BasementBuilds/RobotHandV2/Github STLs/wideWinchThumb (1).stl

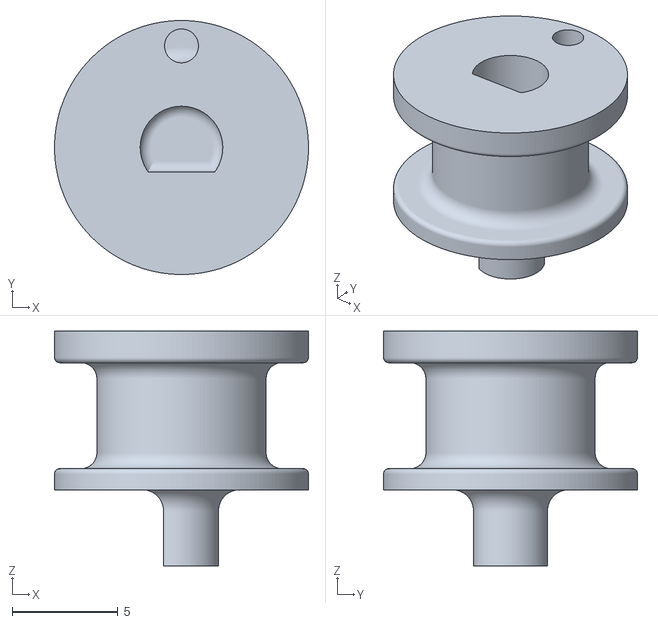
[picture p31: CAD file, 2025-12-30]
Github STLs/wideWinchThumb (1).stl
12.0 x 12.0 x 11.1
