BasementBuilds/RobotHandV2/Github STLs/tpuDigits.stl

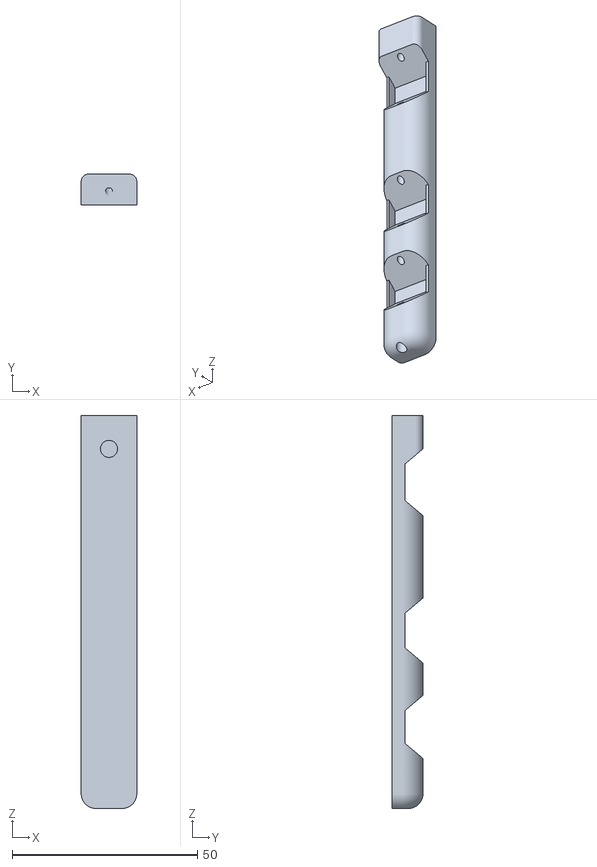
[picture p32: CAD file, 2025-12-30]
Github STLs/tpuDigits.stl
15.0 x 8.35 x 106.0
