BasementBuilds/RobotHandV2/Github STLs/palmBase.stl

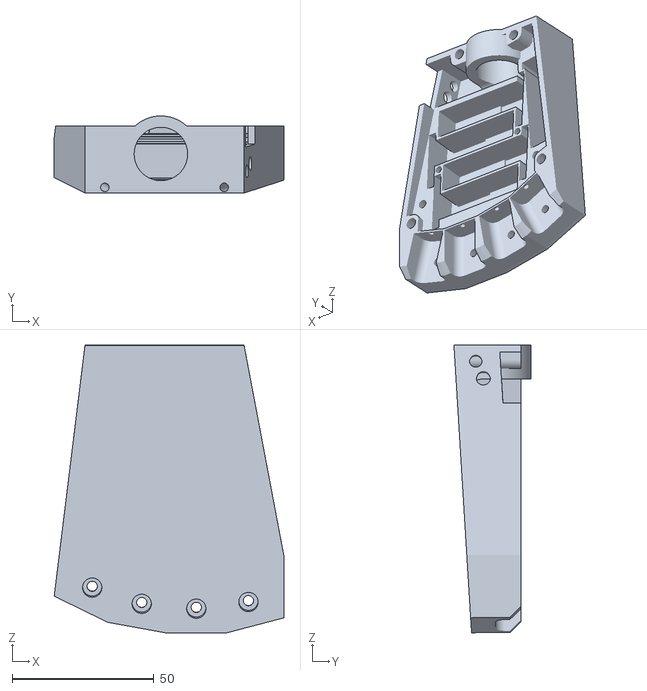
[picture p33: CAD file, 2025-12-30]
Github STLs/palmBase.stl
80.8 x 27.2 x 101.4
