BasementBuilds/RobotHandV2/Github STLs/thumbBase.stl

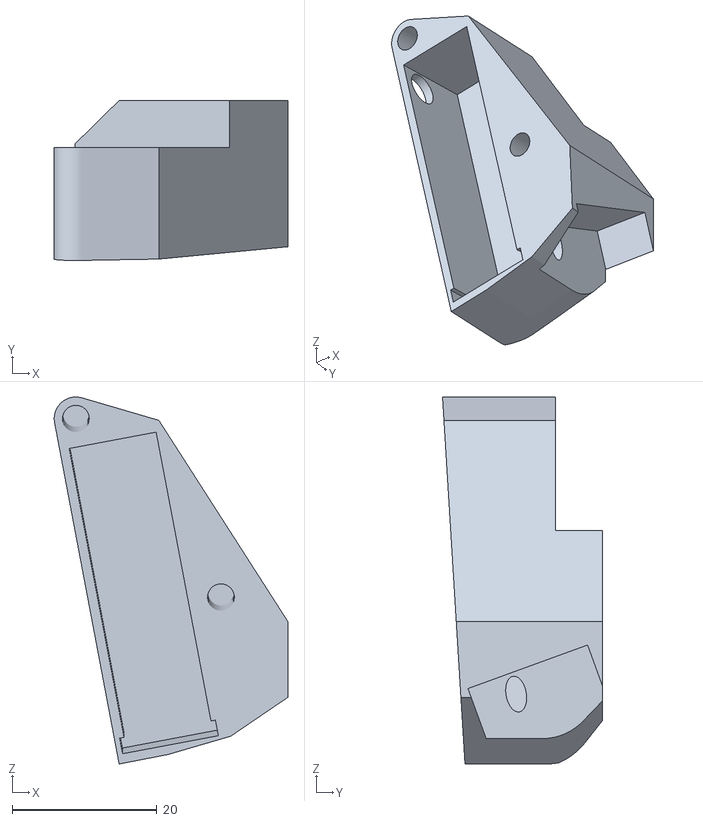
[picture p34: CAD file, 2025-12-30]
Github STLs/thumbBase.stl
32.3 x 22.1 x 50.7
