BasementBuilds/RobotHandV2/Github STLs/detents.stl

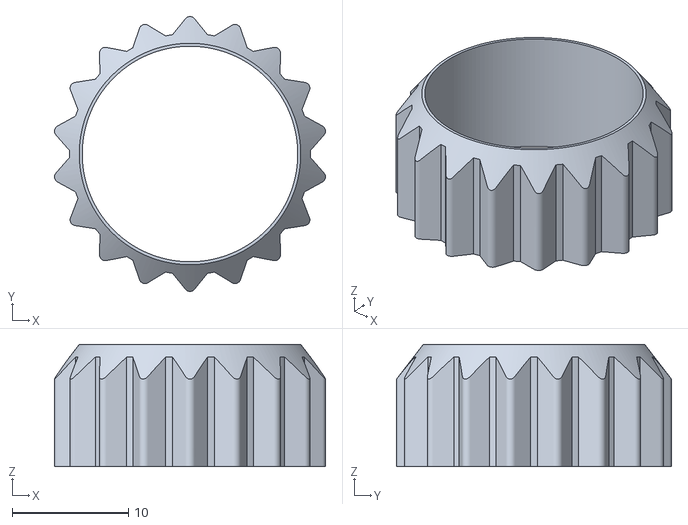
[picture p35: CAD file, 2025-12-30]
Github STLs/detents.stl
23.3 x 23.6 x 10.5
