BasementBuilds/RobotHandV2/Github STLs/forearmCap.stl

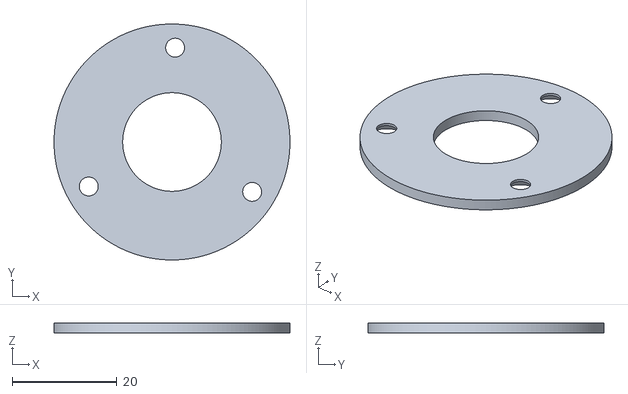
[picture p36: CAD file, 2025-12-30]
Github STLs/forearmCap.stl
45.0 x 45.0 x 2.00
