BasementBuilds/RobotHandV2/Github STLs/threadedInsertHolder.stl

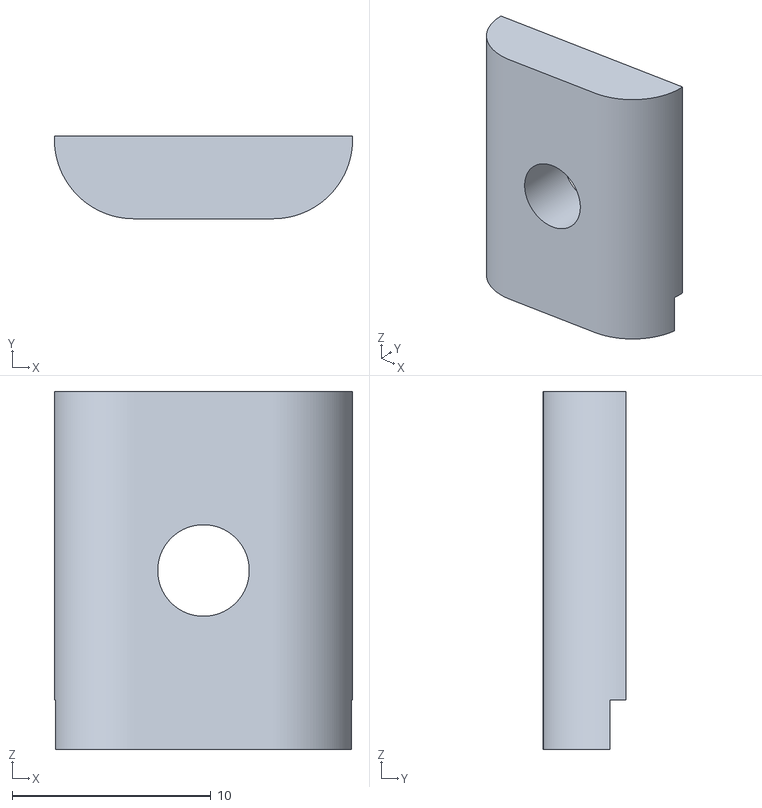
[picture p37: CAD file, 2025-12-30]
Github STLs/threadedInsertHolder.stl
15.0 x 4.15 x 18.0
